naidandemberel/n-watch-v2.0/n-watch v2.0 phone app/Pictures/Screenshot 2022-03-19 152504.png

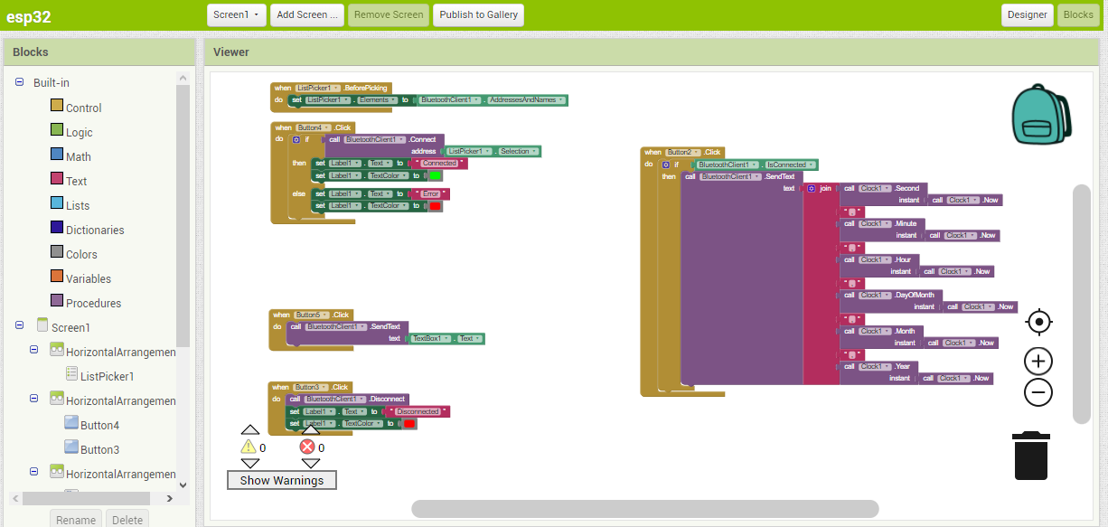
n-watch v2.0 phone app/Pictures/Screenshot 2022-03-19 152504.png
