naidandemberel/n-watch-v2.0/Pictures/20220409_214035.jpg

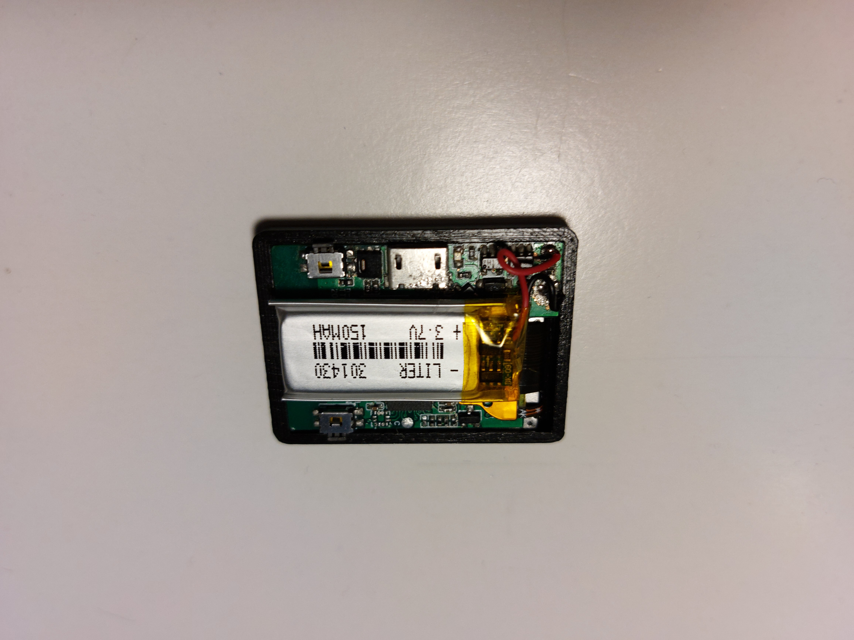
Pictures/20220409_214035.jpg
