naidandemberel/n-watch-v2.0/Pictures/IMG_20211001_234911.jpg

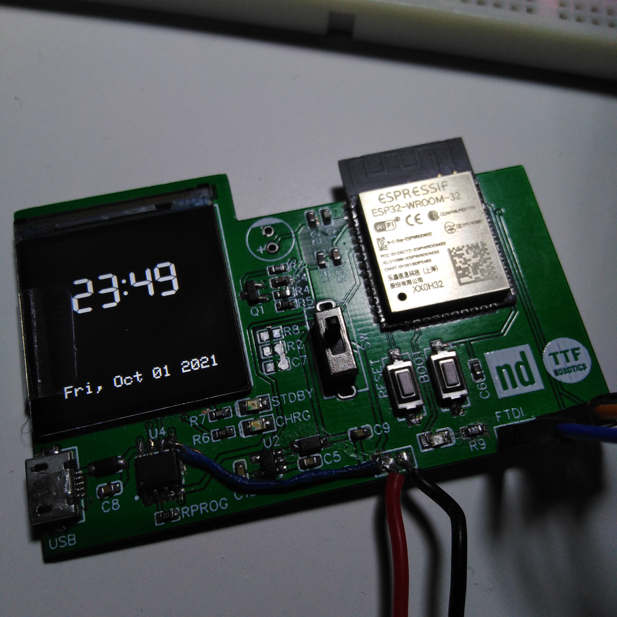
Pictures/IMG_20211001_234911.jpg
