naidandemberel/n-watch-v2.0/Pictures/IMG_20220413_174654.jpg

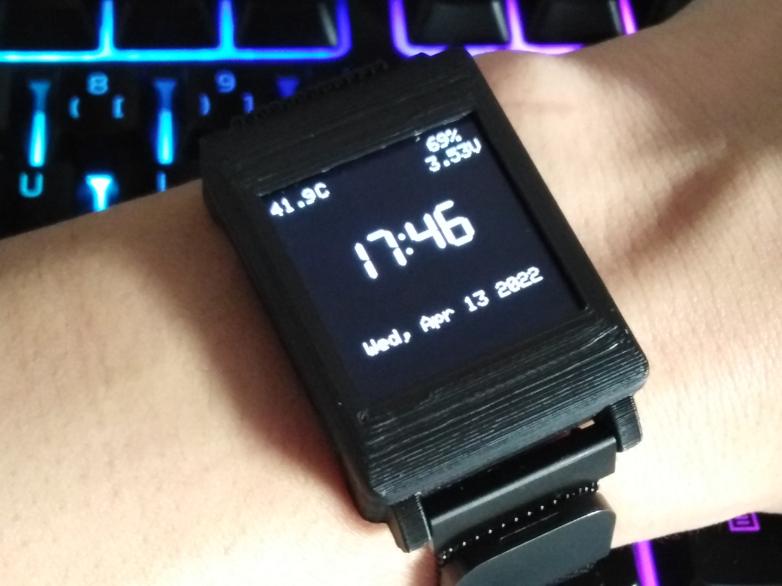
Pictures/IMG_20220413_174654.jpg
