naidandemberel/n-watch-v2.0/Pictures/Screenshot 2021-12-30 210333.png

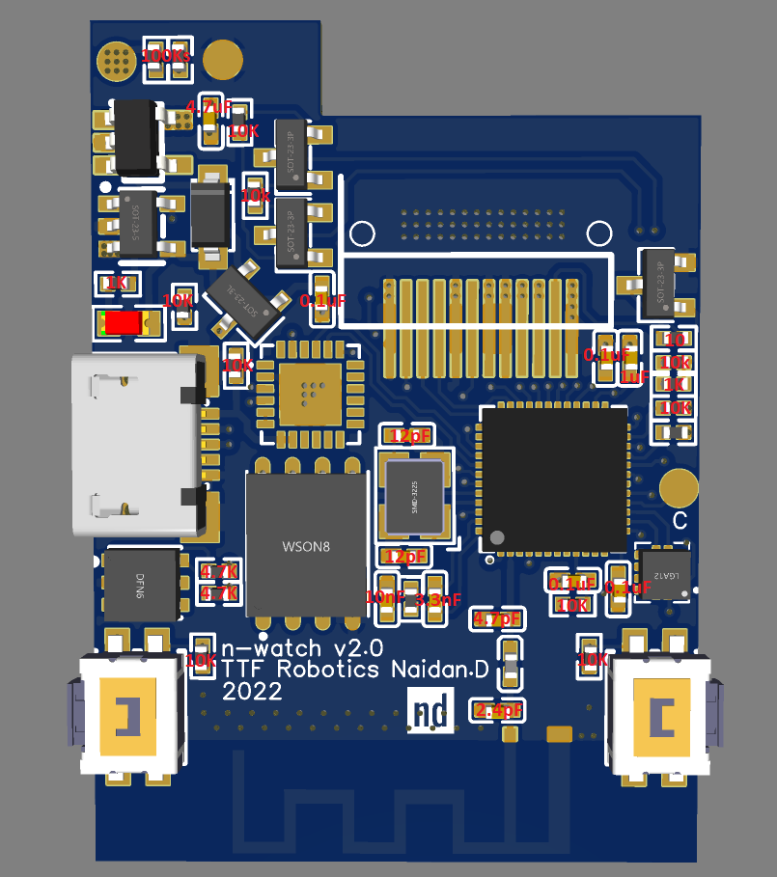
Pictures/Screenshot 2021-12-30 210333.png
